Wikipediano/B3PKey/keyreference.dxf

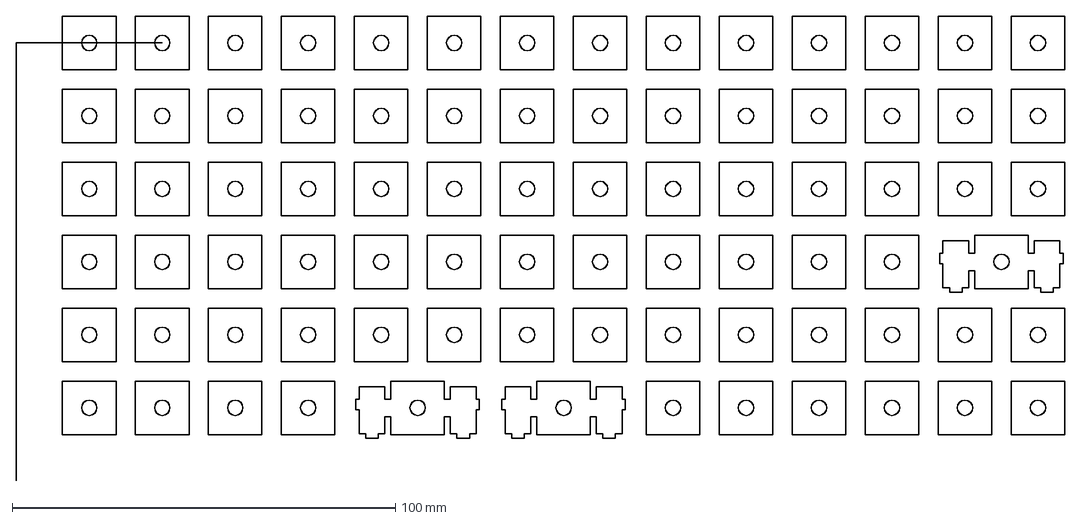
[picture p15: CAD file, 2020-08-15]
keyreference.dxf
273.7 x 121.3 mm
