Wikipediano/B3PKey/outlinewkeys_newsize.dxf

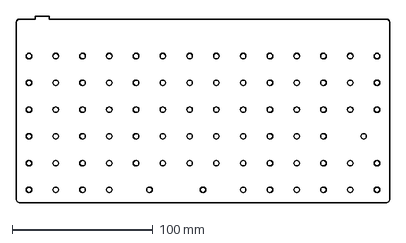
[picture p16: CAD file, 2020-08-15]
outlinewkeys_newsize.dxf
265.7 x 132.4 mm
